TechnologyHill/cloud-chamber-EM-1/CAD/images/components/fan.png

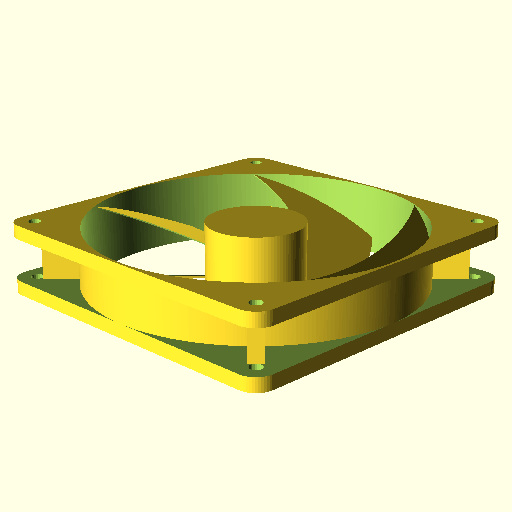
CAD/images/components/fan.png
