TechnologyHill/cloud-chamber-EM-1/CAD/images/components/fitting.png

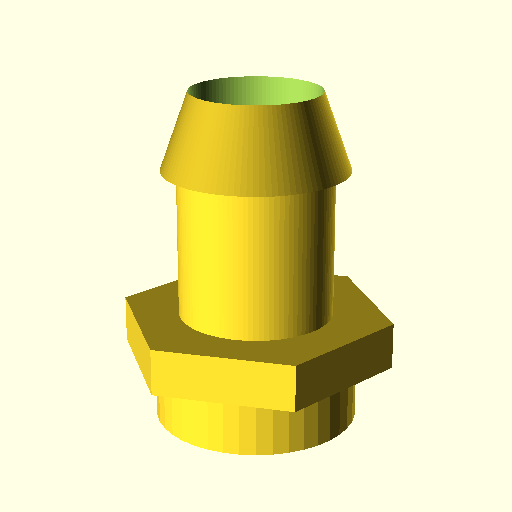
CAD/images/components/fitting.png
