TechnologyHill/cloud-chamber-EM-1/CAD/images/components/frame.png

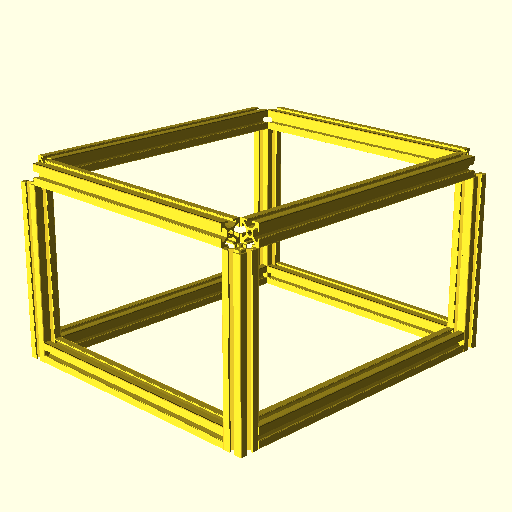
CAD/images/components/frame.png
