TechnologyHill/cloud-chamber-EM-1/CAD/images/components/pump.png

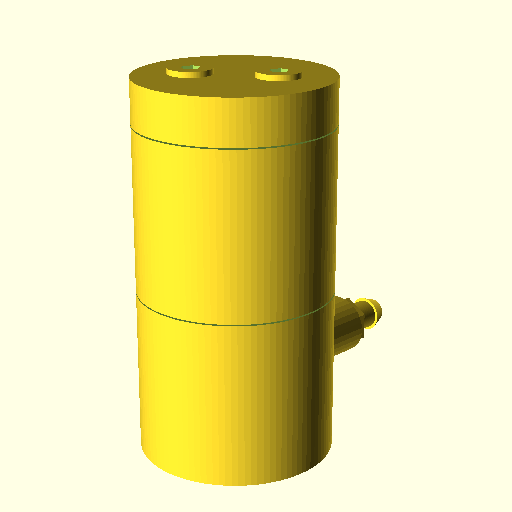
CAD/images/components/pump.png
