TechnologyHill/cloud-chamber-EM-1/CAD/images/components/radiator.png

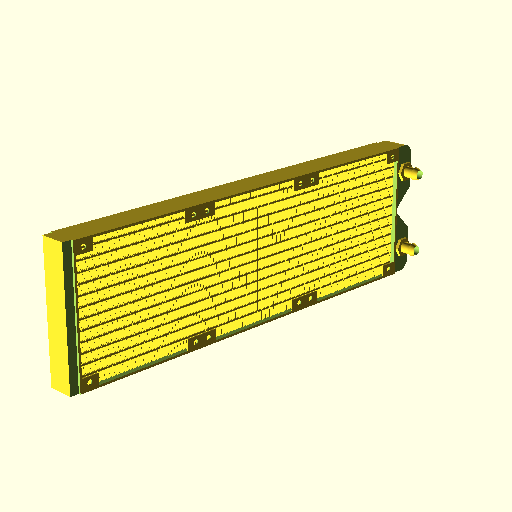
CAD/images/components/radiator.png
