TechnologyHill/cloud-chamber-EM-1/CAD/src/components/frame.scad

//========== ASSEMBLY MODEL ==========//

include <../../parameters.scad>

use <../lib/ALU_profile.scad>
use <../lib/ALU_profile_R.scad>
use <../lib/ALU_profile_3N.scad>
use <../lib/ALU_profile_2NVS.scad>


module frame() {
    translate([chamber_width/2+ALU30_size/2, chamber_deepth/2+ALU30_size/2, -ALU30_size/2])
        rotate([0, 0, 0])
            ALU_profile(size = ALU30_size, height = chamber_height);

    translate([chamber_width/2+ALU30_size/2, -chamber_deepth/2-ALU30_size/2, -ALU30_size/2])
        rotate([0, 0, -90])
            ALU_profile(size = ALU30_size, height = chamber_height);

    translate([-chamber_width/2-ALU30_size/2, chamber_deepth/2+ALU30_size/2, -ALU30_size/2])
        rotate([0, 0, 90])
            ALU_profile(size = ALU30_size, height = chamber_height);

    translate([-chamber_width/2-ALU30_size/2, -chamber_deepth/2-ALU30_size/2, -ALU30_size/2])
        rotate([0, 0, -180])
            ALU_profile(size = ALU30_size, height = chamber_height);



    translate([chamber_width/2+ALU30_size/2, -chamber_deepth/2, 0])
        rotate([-90, 0, 0])
            ALU_profile(size = ALU30_size, height = chamber_deepth);

    translate([chamber_width/-2-ALU30_size/2, -chamber_deepth/2, 0])
        rotate([-90, 90, 0])
            ALU_profile(size = ALU30_size, height = chamber_deepth);

    translate([-chamber_width/2, -chamber_deepth/2-ALU30_size/2, 0])
        rotate([-90, 0, -90])
            ALU_profile(size = ALU30_size, height = chamber_width);

    translate([-chamber_width/2, chamber_deepth/2+ALU30_size/2, 0])
        rotate([0, 90, 0])
            ALU_profile(size = ALU30_size, height = chamber_width);


    translate([0, 0, chamber_height]) {
        rotate([0, 0, 0]) {
        translate([chamber_width/2+ALU30_size/2, -chamber_deepth/2, 0])
            rotate([-90, 0, 0])
                ALU_profile(size = ALU30_size, height = chamber_deepth);

        translate([chamber_width/-2-ALU30_size/2, -chamber_deepth/2, 0])
            rotate([-90, 90, 0])
                ALU_profile(size = ALU30_size, height = chamber_deepth);

        translate([-chamber_width/2, -chamber_deepth/2-ALU30_size/2, 0])
            rotate([-90, 0, -90])
                ALU_profile(size = ALU30_size, height = chamber_width);

        translate([-chamber_width/2, chamber_deepth/2+ALU30_size/2, 0])
            rotate([0, 90, 0])
                ALU_profile(size = ALU30_size, height = chamber_width);
        }
    }
}

frame();
